junhua-best/H-Watch/PROGRAM/LCD/lcd.c

#include "lcd.h"
#include "lcd_init.h"
#include "lcdfont.h"

#include "spi.h"

/******************************************************************************
      函数说明：在指定区域填充颜色
      入口数据：xsta,ysta   起始坐标
                xend,yend   终止坐标
								color       要填充的颜色
      返回值：  无
******************************************************************************/

void LCD_Fill(uint16_t xsta,uint16_t ysta,uint16_t xend,uint16_t yend,uint16_t color)
{      
	uint16_t i,j; 
	uint8_t an[(xend-xsta)*2];
	uint32_t k=0;
	
	LCD_Address_Set(xsta,ysta,xend-1,yend-1);//设置显示范围
	
	for(i=ysta;i<yend;i++)
	{													   	 	
		for(j=xsta;j<xend;j++)
		{
			an[k] = color>>8;
			an[k+1]= color - (an[k]<<8);
			k=k+2;		
		}
		HAL_SPI_Transmit(&hspi1,an,(xend-xsta)*2,10);//发送数据	
		k=0;
	}
		  	    
}


/******************************************************************************
      函数说明：在指定区域填充颜色
      入口数据：xsta,ysta   起始坐标
                xend,yend   终止坐标
								color       要填充的颜色
         原版函数
******************************************************************************/
/*
void LCD_Fill(uint16_t xsta,uint16_t ysta,uint16_t xend,uint16_t yend,uint16_t color)
{          
	uint16_t i,j; 
	LCD_Address_Set(xsta,ysta,xend-1,yend-1);//设置显示范围
	for(i=ysta;i<yend;i++)
	{													   	 	
		for(j=xsta;j<xend;j++)
		{
			LCD_WR_DATA(color);
		}
	} 					  	    
}
*/
/******************************************************************************
      函数说明：在指定位置画点
      入口数据：x,y 画点坐标
                color 点的颜色
      返回值：  无
******************************************************************************/
void LCD_DrawPoint(uint16_t x,uint16_t y,uint16_t color)
{
	LCD_Address_Set(x,y,x,y);//设置光标位置 
	LCD_WR_DATA(color);
} 


/******************************************************************************
      函数说明：画线
      入口数据：x1,y1   起始坐标
                x2,y2   终止坐标
                color   线的颜色
      返回值：  无
******************************************************************************/
void LCD_DrawLine(uint16_t x1,uint16_t y1,uint16_t x2,uint16_t y2,uint16_t color)
{
	uint16_t t; 
	int xerr=0,yerr=0,delta_x,delta_y,distance;
	int incx,incy,uRow,uCol;
	delta_x=x2-x1; //计算坐标增量 
	delta_y=y2-y1;
	uRow=x1;//画线起点坐标
	uCol=y1;
	if(delta_x>0)incx=1; //设置单步方向 
	else if (delta_x==0)incx=0;//垂直线 
	else {incx=-1;delta_x=-delta_x;}
	if(delta_y>0)incy=1;
	else if (delta_y==0)incy=0;//水平线 
	else {incy=-1;delta_y=-delta_y;}
	if(delta_x>delta_y)distance=delta_x; //选取基本增量坐标轴 
	else distance=delta_y;
	for(t=0;t<distance+1;t++)
	{
		LCD_DrawPoint(uRow,uCol,color);//画点
		xerr+=delta_x;
		yerr+=delta_y;
		if(xerr>distance)
		{
			xerr-=distance;
			uRow+=incx;
		}
		if(yerr>distance)
		{
			yerr-=distance;
			uCol+=incy;
		}
	}
}


/******************************************************************************
      函数说明：画矩形
      入口数据：x1,y1   起始坐标
                x2,y2   终止坐标
                color   矩形的颜色
      返回值：  无
******************************************************************************/
void LCD_DrawRectangle(uint16_t x1, uint16_t y1, uint16_t x2, uint16_t y2,uint16_t color)
{
	LCD_DrawLine(x1,y1,x2,y1,color);
	LCD_DrawLine(x1,y1,x1,y2,color);
	LCD_DrawLine(x1,y2,x2,y2,color);
	LCD_DrawLine(x2,y1,x2,y2,color);
}


/******************************************************************************
      函数说明：画圆
      入口数据：x0,y0   圆心坐标
                r       半径
                color   圆的颜色
      返回值：  无
******************************************************************************/
void Draw_Circle(uint16_t x0,uint16_t y0,uint8_t r,uint16_t color)
{
	int a,b;
	a=0;b=r;	  
	while(a<=b)
	{
		LCD_DrawPoint(x0-b,y0-a,color);             //3           
		LCD_DrawPoint(x0+b,y0-a,color);             //0           
		LCD_DrawPoint(x0-a,y0+b,color);             //1                
		LCD_DrawPoint(x0-a,y0-b,color);             //2             
		LCD_DrawPoint(x0+b,y0+a,color);             //4               
		LCD_DrawPoint(x0+a,y0-b,color);             //5
		LCD_DrawPoint(x0+a,y0+b,color);             //6 
		LCD_DrawPoint(x0-b,y0+a,color);             //7
		a++;
		if((a*a+b*b)>(r*r))//判断要画的点是否过远
		{
			b--;
		}
	}
}

/******************************************************************************
      函数说明：显示汉字串
      入口数据：x,y显示坐标
                *s 要显示的汉字串
                fc 字的颜色
                bc 字的背景色
                sizey 字号 可选 16 24 32
                mode:  0非叠加模式  1叠加模式
      返回值：  无
******************************************************************************/
void LCD_ShowChinese(uint16_t x,uint16_t y,uint8_t *s,uint16_t fc,uint16_t bc,uint8_t sizey,uint8_t mode)
{
	while(*s!=0)
	{
		if(sizey==12) LCD_ShowChinese12x12(x,y,s,fc,bc,sizey,mode);
		else if(sizey==16) LCD_ShowChinese16x16(x,y,s,fc,bc,sizey,mode);
		else if(sizey==24) LCD_ShowChinese24x24(x,y,s,fc,bc,sizey,mode);
		else if(sizey==32) LCD_ShowChinese32x32(x,y,s,fc,bc,sizey,mode);
		else return;
		s+=2;
		x+=sizey;
	}
}

/******************************************************************************
      函数说明：显示单个12x12汉字
      入口数据：x,y显示坐标
                *s 要显示的汉字
                fc 字的颜色
                bc 字的背景色
                sizey 字号
                mode:  0非叠加模式  1叠加模式
      返回值：  无
******************************************************************************/
void LCD_ShowChinese12x12(uint16_t x,uint16_t y,uint8_t *s,uint16_t fc,uint16_t bc,uint8_t sizey,uint8_t mode)
{
	uint8_t i,j,m=0;
	uint16_t k;
	uint16_t HZnum;//汉字数目
	uint16_t TypefaceNum;//一个字符所占字节大小
	uint16_t x0=x;
	TypefaceNum=(sizey/8+((sizey%8)?1:0))*sizey;
	                         
	HZnum=sizeof(tfont12)/sizeof(typFNT_GB12);	//统计汉字数目
	for(k=0;k<HZnum;k++) 
	{
		if((tfont12[k].Index[0]==*(s))&&(tfont12[k].Index[1]==*(s+1)))
		{ 	
			LCD_Address_Set(x,y,x+sizey-1,y+sizey-1);
			for(i=0;i<TypefaceNum;i++)
			{
				for(j=0;j<8;j++)
				{	
					if(!mode)//非叠加方式
					{
						if(tfont12[k].Msk[i]&(0x01<<j))LCD_WR_DATA(fc);
						else LCD_WR_DATA(bc);
						m++;
						if(m%sizey==0)
						{
							m=0;
							break;
						}
					}
					else//叠加方式
					{
						if(tfont12[k].Msk[i]&(0x01<<j))	LCD_DrawPoint(x,y,fc);//画一个点
						x++;
						if((x-x0)==sizey)
						{
							x=x0;
							y++;
							break;
						}
					}
				}
			}
		}				  	
		continue;  //查找到对应点阵字库立即退出，防止多个汉字重复取模带来影响
	}
} 

/******************************************************************************
      函数说明：显示单个16x16汉字
      入口数据：x,y显示坐标
                *s 要显示的汉字
                fc 字的颜色
                bc 字的背景色
                sizey 字号
                mode:  0非叠加模式  1叠加模式
      返回值：  无
******************************************************************************/
void LCD_ShowChinese16x16(uint16_t x,uint16_t y,uint8_t *s,uint16_t fc,uint16_t bc,uint8_t sizey,uint8_t mode)
{
	uint8_t i,j,m=0;
	uint16_t k;
	uint16_t HZnum;//汉字数目
	uint16_t TypefaceNum;//一个字符所占字节大小
	uint16_t x0=x;
  TypefaceNum=(sizey/8+((sizey%8)?1:0))*sizey;
	HZnum=sizeof(tfont16)/sizeof(typFNT_GB16);	//统计汉字数目
	for(k=0;k<HZnum;k++) 
	{
		if ((tfont16[k].Index[0]==*(s))&&(tfont16[k].Index[1]==*(s+1)))
		{ 	
			LCD_Address_Set(x,y,x+sizey-1,y+sizey-1);
			for(i=0;i<TypefaceNum;i++)
			{
				for(j=0;j<8;j++)
				{	
					if(!mode)//非叠加方式
					{
						if(tfont16[k].Msk[i]&(0x01<<j))LCD_WR_DATA(fc);
						else LCD_WR_DATA(bc);
						m++;
						if(m%sizey==0)
						{
							m=0;
							break;
						}
					}
					else//叠加方式
					{
						if(tfont16[k].Msk[i]&(0x01<<j))	LCD_DrawPoint(x,y,fc);//画一个点
						x++;
						if((x-x0)==sizey)
						{
							x=x0;
							y++;
							break;
						}
					}
				}
			}
		}				  	
		continue;  //查找到对应点阵字库立即退出，防止多个汉字重复取模带来影响
	}
} 


/******************************************************************************
      函数说明：显示单个24x24汉字
      入口数据：x,y显示坐标
                *s 要显示的汉字
                fc 字的颜色
                bc 字的背景色
                sizey 字号
                mode:  0非叠加模式  1叠加模式
      返回值：  无
******************************************************************************/
void LCD_ShowChinese24x24(uint16_t x,uint16_t y,uint8_t *s,uint16_t fc,uint16_t bc,uint8_t sizey,uint8_t mode)
{
	uint8_t i,j,m=0;
	uint16_t k;
	uint16_t HZnum;//汉字数目
	uint16_t TypefaceNum;//一个字符所占字节大小
	uint16_t x0=x;
	TypefaceNum=(sizey/8+((sizey%8)?1:0))*sizey;
	HZnum=sizeof(tfont24)/sizeof(typFNT_GB24);	//统计汉字数目
	for(k=0;k<HZnum;k++) 
	{
		if ((tfont24[k].Index[0]==*(s))&&(tfont24[k].Index[1]==*(s+1)))
		{ 	
			LCD_Address_Set(x,y,x+sizey-1,y+sizey-1);
			for(i=0;i<TypefaceNum;i++)
			{
				for(j=0;j<8;j++)
				{	
					if(!mode)//非叠加方式
					{
						if(tfont24[k].Msk[i]&(0x01<<j))LCD_WR_DATA(fc);
						else LCD_WR_DATA(bc);
						m++;
						if(m%sizey==0)
						{
							m=0;
							break;
						}
					}
					else//叠加方式
					{
						if(tfont24[k].Msk[i]&(0x01<<j))	LCD_DrawPoint(x,y,fc);//画一个点
						x++;
						if((x-x0)==sizey)
						{
							x=x0;
							y++;
							break;
						}
					}
				}
			}
		}				  	
		continue;  //查找到对应点阵字库立即退出，防止多个汉字重复取模带来影响
	}
} 

/******************************************************************************
      函数说明：显示单个32x32汉字
      入口数据：x,y显示坐标
                *s 要显示的汉字
                fc 字的颜色
                bc 字的背景色
                sizey 字号
                mode:  0非叠加模式  1叠加模式
      返回值：  无
******************************************************************************/
void LCD_ShowChinese32x32(uint16_t x,uint16_t y,uint8_t *s,uint16_t fc,uint16_t bc,uint8_t sizey,uint8_t mode)
{
	uint8_t i,j,m=0;
	uint16_t k;
	uint16_t HZnum;//汉字数目
	uint16_t TypefaceNum;//一个字符所占字节大小
	uint16_t x0=x;
	TypefaceNum=(sizey/8+((sizey%8)?1:0))*sizey;
	HZnum=sizeof(tfont32)/sizeof(typFNT_GB32);	//统计汉字数目
	for(k=0;k<HZnum;k++) 
	{
		if ((tfont32[k].Index[0]==*(s))&&(tfont32[k].Index[1]==*(s+1)))
		{ 	
			LCD_Address_Set(x,y,x+sizey-1,y+sizey-1);
			for(i=0;i<TypefaceNum;i++)
			{
				for(j=0;j<8;j++)
				{	
					if(!mode)//非叠加方式
					{
						if(tfont32[k].Msk[i]&(0x01<<j))LCD_WR_DATA(fc);
						else LCD_WR_DATA(bc);
						m++;
						if(m%sizey==0)
						{
							m=0;
							break;
						}
					}
					else//叠加方式
					{
						if(tfont32[k].Msk[i]&(0x01<<j))	LCD_DrawPoint(x,y,fc);//画一个点
						x++;
						if((x-x0)==sizey)
						{
							x=x0;
							y++;
							break;
						}
					}
				}
			}
		}				  	
		continue;  //查找到对应点阵字库立即退出，防止多个汉字重复取模带来影响
	}
}


/******************************************************************************
      函数说明：显示单个字符
      入口数据：x,y显示坐标
                num 要显示的字符
                fc 字的颜色
                bc 字的背景色
                sizey 字号
                mode:  0非叠加模式  1叠加模式
      返回值：  无
******************************************************************************/
void LCD_ShowChar(uint16_t x,uint16_t y,uint8_t num,uint16_t fc,uint16_t bc,uint8_t sizey,uint8_t mode)
{
	uint8_t temp,sizex,t,m=0;
	uint16_t i,TypefaceNum;//一个字符所占字节大小
	uint16_t x0=x;
	sizex=sizey/2;
	TypefaceNum=(sizex/8+((sizex%8)?1:0))*sizey;
	num=num-' ';    //得到偏移后的值
	LCD_Address_Set(x,y,x+sizex-1,y+sizey-1);  //设置光标位置 
	for(i=0;i<TypefaceNum;i++)
	{ 
		if(sizey==12)temp=ascii_1206[num][i];		       //调用6x12字体
		else if(sizey==16)temp=ascii_1608[num][i];		 //调用8x16字体
		else if(sizey==24)temp=ascii_2412[num][i];		 //调用12x24字体
		else if(sizey==32)temp=ascii_3216[num][i];		 //调用16x32字体
		else return;
		for(t=0;t<8;t++)
		{
			if(!mode)//非叠加模式
			{
				if(temp&(0x01<<t))LCD_WR_DATA(fc);
				else LCD_WR_DATA(bc);
				m++;
				if(m%sizex==0)
				{
					m=0;
					break;
				}
			}
			else//叠加模式
			{
				if(temp&(0x01<<t))LCD_DrawPoint(x,y,fc);//画一个点
				x++;
				if((x-x0)==sizex)
				{
					x=x0;
					y++;
					break;
				}
			}
		}
	}   	 	  
}


/******************************************************************************
      函数说明：显示字符串
      入口数据：x,y显示坐标
                *p 要显示的字符串
                fc 字的颜色
                bc 字的背景色
                sizey 字号
                mode:  0非叠加模式  1叠加模式
      返回值：  无
******************************************************************************/
void LCD_ShowString(uint16_t x,uint16_t y,const uint8_t *p,uint16_t fc,uint16_t bc,uint8_t sizey,uint8_t mode)
{         
	while(*p!='\0')
	{       
		LCD_ShowChar(x,y,*p,fc,bc,sizey,mode);
		x+=sizey/2;
		p++;
	}  
}


/******************************************************************************
      函数说明：显示数字
      入口数据：m底数，n指数
      返回值：  无
******************************************************************************/
uint32_t mypow(uint8_t m,uint8_t n)
{
	uint32_t result=1;	 
	while(n--)result*=m;
	return result;
}


/******************************************************************************
      函数说明：显示整数变量
      入口数据：x,y显示坐标
                num 要显示整数变量
                len 要显示的位数
                fc 字的颜色
                bc 字的背景色
                sizey 字号
      返回值：  无
******************************************************************************/
void LCD_ShowIntNum(uint16_t x,uint16_t y,uint16_t num,uint8_t len,uint16_t fc,uint16_t bc,uint8_t sizey,uint8_t mode)
{         	
	uint8_t t,temp;
	uint8_t enshow=0;
	uint8_t sizex=sizey/2;
	for(t=0;t<len;t++)
	{
		temp=(num/mypow(10,len-t-1))%10;
		if(enshow==0&&t<(len-1))
		{
			if(temp==0)
			{
				LCD_ShowChar(x+t*sizex,y,'0',fc,bc,sizey,mode);
				continue;
			}else enshow=1; 
		 	 
		}
	 	LCD_ShowChar(x+t*sizex,y,temp+48,fc,bc,sizey,mode);
	}
} 


/******************************************************************************
      函数说明：显示两位小数变量
      入口数据：x,y显示坐标
                num 要显示小数变量
                len 要显示的位数
                fc 字的颜色
                bc 字的背景色
                sizey 字号
      返回值：  无
******************************************************************************/
void LCD_ShowFloatNum1(uint16_t x,uint16_t y,float num,uint8_t len,uint16_t fc,uint16_t bc,uint8_t sizey,uint8_t mode)
{         	
	uint8_t t,temp,sizex;
	int num1;
	sizex=sizey/2;
	num1=num*100;
	for(t=0;t<len;t++)
	{
		temp=(num1/mypow(10,len-t-1))%10;
		if(t==(len-2))
		{
			LCD_ShowChar(x+(len-2)*sizex,y,'.',fc,bc,sizey,mode);
			t++;
			len+=1;
		}
	 	LCD_ShowChar(x+t*sizex,y,temp+48,fc,bc,sizey,mode);
	}
}


/******************************************************************************
      函数说明：显示图片
      入口数据：x,y起点坐标
                length 图片长度
                width  图片宽度
                pic[]  图片数组    
      返回值：  无
******************************************************************************/
void LCD_ShowPicture(uint16_t x,uint16_t y,uint16_t length,uint16_t width,const uint8_t pic[])
{
	uint32_t i,j;
	
	uint8_t an[width*2];
	
	LCD_Address_Set(x,y,x+length-1,y+width-1);
	
	for(i=0;i<length;i++)
	{
		for(j=0;j<width*2;j++)
		{
			an[j] = pic[j+i*width*2];
		}
		HAL_SPI_Transmit(&hspi1,an,width*2,10);//发送数据
	}			
}

//{
//	uint16_t i,j;
//	uint32_t k=0;
//	
//	uint8_t an[width];
//	
//	LCD_Address_Set(x,y,x+length-1,y+width-1);
//	
//	for(i=0;i<length;i++)
//	{
//		for(j=0;j<width;j++)
//		{
//			LCD_WR_DATA8(pic[k*2]);
//			LCD_WR_DATA8(pic[k*2+1]);
//			k++;
//		}
//	}			
//}HAL_SPI_Transmit(&hspi1,an,length*width,10);//发送数据
/******************************************************************************
      函数说明：显示图片
      入口数据：x,y起点坐标
                length 图片长度
                width  图片宽度
                pic[]  图片数组    
      返回值：  无
******************************************************************************/
void LCD_ShowPicture_no_wite(uint16_t x,uint16_t y,uint16_t length,uint16_t width,const uint8_t pic[])
{
	uint16_t i,j;
	uint32_t k=0;
	uint8_t dat_buffer[2];
	for(i=y; i<y+width; i++) //根据显示原理，按照先行数后列数进行刷新
	{
		for(j=x; j<x+length; j++)//循环每行上面的像素点
		{
			if(pic[k]!= 0xFF && pic[k+1]!= 0xFF)
			{	
				LCD_Address_Set(j,i,j,i);//设置光标位置 //注意这里的横纵坐标是反着的
//				LCD_Writ_Bus(pic[k]);
//				LCD_Writ_Bus(pic[k+1]);
				dat_buffer[0] = pic[k];
				dat_buffer[1] = pic[k+1];
				HAL_SPI_Transmit_DMA(&hspi1,dat_buffer,2);//发送数据	
			}
			k = k+2;
		}
	}				
}

/******************************************************************************
      函数说明：显示图片
      入口数据：x,y起点坐标
                length 图片长度
                width  图片宽度
                pic[]  图片数组    
      返回值：  无
******************************************************************************/
void LCD_ShowPicture_no(uint16_t x,uint16_t y,uint16_t length,uint16_t width,const uint8_t pic[])
{
	uint16_t i,j;
	uint32_t k=0;
	uint8_t dat_buffer[2];
	
	for(i=y; i<y+width; i++) //根据显示原理，按照先行数后列数进行刷新
	{
		for(j=x; j<x+length; j++)//循环每行上面的像素点
		{
			LCD_Address_Set(j,i,j,i);//设置光标位置 //注意这里的横纵坐标是反着的
//			//列地址设置
//			LCD_DC_Clr();//写命令
//			LCD_Writ_Bus(0x2a);
//			LCD_DC_Set();//写数据
//					
//			dat_buffer[0] = j;
//			dat_buffer[1] = j;	
//			HAL_SPI_Transmit(&hspi1,dat_buffer,2,10);//发送数据
//			
//			
//			//行地址设置
//			LCD_DC_Clr();//写命令
//			LCD_Writ_Bus(0x2b);
//			LCD_DC_Set();//写数据
//			
//			
//			dat_buffer[0] = i+80;
//			dat_buffer[1] = i+80;	
//			HAL_SPI_Transmit(&hspi1,dat_buffer,2,10);//发送数据	
//			
//			//储存器写
//			LCD_DC_Clr();//写命令
//			LCD_Writ_Bus(0x2c);
//			LCD_DC_Set();//写数据
			
			
			dat_buffer[0] = pic[k];
			dat_buffer[1] = pic[k+1];
				
			HAL_SPI_Transmit(&hspi1,dat_buffer,2,10);//发送数据
			
					
			k = k+2;
		}
	}				
}

/******************************************************************************
      函数说明：显示图片
      入口数据：x,y起点坐标
                length 图片长度
                width  图片宽度
                pic[]  图片数组    
      返回值：  无
******************************************************************************/
void LCD_ShowPicture_clear(uint16_t x,uint16_t y,uint16_t length,uint16_t width,const uint8_t pic[])
{
	uint16_t i,j;
	uint32_t k=0;
	uint8_t dat_buffer[2];
	
	for(i=y; i<y+width; i++) //根据显示原理，按照先行数后列数进行刷新
	{
		for(j=x; j<x+length; j++)//循环每行上面的像素点
		{
			if(pic[k]!= 0xFF && pic[k+1]!= 0xFF)
			{	
//				LCD_Address_Set(j,i,j,i);//设置光标位置 //注意这里的横纵坐标是反着的
//				LCD_Writ_Bus(pic[k]);
//				LCD_Writ_Bus(pic[k+1]);
				
				//列地址设置
				LCD_DC_Clr();//写命令
				LCD_Writ_Bus(0x2a);
				LCD_DC_Set();//写数据
						
				dat_buffer[0] = j;
				dat_buffer[1] = j;	
				HAL_SPI_Transmit(&hspi1,dat_buffer,2,10);//发送数据
				
				
				//行地址设置
				LCD_DC_Clr();//写命令
				LCD_Writ_Bus(0x2b);
				LCD_DC_Set();//写数据
				
				
				dat_buffer[0] = i+80;
				dat_buffer[1] = i+80;	
				HAL_SPI_Transmit(&hspi1,dat_buffer,2,10);//发送数据	
				
				//储存器写
				LCD_DC_Clr();//写命令
				LCD_Writ_Bus(0x2c);
				LCD_DC_Set();//写数据
				
				
				dat_buffer[0] = pic[k];
				dat_buffer[1] = pic[k+1];
					
				HAL_SPI_Transmit(&hspi1,dat_buffer,2,10);//发送数据

			}
			k = k+2;
		}
	}				
}

//在指定区域内填充指定颜色块			 junhua 
//(sx,sy),(ex,ey):填充矩形对角坐标,区域大小为:(ex-sx+1)*(ey-sy+1)   
//color:要填充的颜色
/*
void LCD_Color_Fill(uint16_t sx,uint16_t sy,uint16_t ex,uint16_t ey,uint16_t *color)
{
	uint16_t height,width;
	uint16_t i,j;
	width=ex-sx+1; 			//得到填充的宽度
	height=ey-sy+1;			//高度
	//LCD_Address_Set(sx,sy,ex-1,ey-1);//设置显示范围
	//uint8_t an[(ex-sx)*2];
	//uint32_t k=0;
 	for(i=0;i<height;i++)
	{
 		
		for(j=0;j<width;j++)
		{
			
			LCD_DrawPoint(sx+j,sy+i, color[i*width+j]);
		}
		
	}
}
*/

//这种更快 设置范围只能一行一行的来

void LCD_Color_Fill(uint16_t sx,uint16_t sy,uint16_t ex,uint16_t ey,uint16_t *color)
{
	uint16_t height,width;
	uint16_t i,j;
	width=ex-sx+1; 			//得到填充的宽度
	height=ey-sy+1;			//高度
	//LCD_Address_Set(sx,sy,ex-1,ey-1);//设置显示范围
	uint8_t an[(ex-sx)*2];
	
	uint32_t k=0;
 	for(i=0;i<height;i++)
	{
 		
		LCD_Address_Set(sx,sy+i,ex-1,sy+i);//设置光标位置 
		for(j=0;j<width;j++)
		{
			
			//LCD_WR_DATA(color[i*width+j]);
			//写入数据  参考原来LCD_Fill的写法
			
			an[k] = color[i*width+j]>>8;
			an[k+1]= color[i*width+j] - (an[k]<<8);
			k=k+2;		
		
		}
		HAL_SPI_Transmit(&hspi1,an,(ex-sx)*2,10);//发送数据	
		k=0;
	}
}
