junhua-best/H-Watch/PROGRAM/LCD/pic.h

#ifndef __PIC_H
#define __PIC_H

const unsigned char gImage_shadian[512] = { /* 0X10,0X10,0X00,0X10,0X00,0X10,0X01,0X1B, */
0XFF,0X80,0XFF,0X80,0XFF,0X80,0XFF,0X80,0XFF,0X80,0XFF,0X80,0XFF,0X80,0XFF,0X80,
0XFF,0X80,0XFF,0X80,0XFF,0X62,0XFF,0X23,0XF6,0XD4,0XFF,0X80,0XFF,0X80,0XFF,0X80,
0XFF,0X80,0XFF,0X80,0XFF,0X80,0XFF,0X80,0XFF,0X80,0XFF,0X80,0XFF,0X80,0XFF,0X80,
0XFF,0X80,0XFF,0X02,0XED,0X4E,0XF5,0XEE,0XFF,0X80,0XFF,0X80,0XFF,0X80,0XFF,0X80,
0XFF,0X80,0XFF,0X80,0XFF,0X80,0XFF,0X80,0XFF,0X80,0XFF,0X80,0XFF,0X80,0XFF,0X80,
0XFF,0X00,0XEB,0X87,0XF4,0XC7,0XFF,0X40,0XFF,0X80,0XFF,0X80,0XFF,0X80,0XFF,0X80,
0XFF,0X80,0XFF,0X80,0XFF,0X80,0XFF,0X80,0XFF,0X80,0XFF,0X80,0XFF,0X80,0XFF,0X80,
0XD9,0X00,0XEB,0X84,0XFF,0X40,0XFF,0X80,0XFF,0X80,0XFF,0X80,0XFF,0X80,0XFF,0X80,
0XFF,0X80,0XFF,0X80,0XFF,0X80,0XFF,0X80,0XFF,0X80,0XFF,0X41,0XF5,0X6C,0XD1,0X04,
0XEB,0XA7,0XFF,0X80,0XFF,0X80,0XFF,0X80,0XFF,0X80,0XFF,0X80,0XFF,0X80,0XFF,0X80,
0XFF,0X80,0XFF,0X80,0XFF,0X80,0XFF,0X80,0XFE,0XE9,0XEB,0XE4,0XD9,0X04,0XEC,0X30,
0XF6,0X87,0XFE,0X67,0XFE,0X87,0XF6,0X67,0XF6,0X26,0XFE,0XE5,0XFF,0X80,0XFF,0X80,
0XFF,0X80,0XFF,0X80,0XFF,0X80,0XFD,0X68,0XDA,0X49,0XD0,0X20,0XD8,0X41,0XDA,0X08,
0XD9,0XE7,0XD9,0XC7,0XE1,0XC7,0XD9,0XC7,0XD9,0XC7,0XFD,0XEC,0XFF,0X80,0XFF,0X80,
0XFF,0X80,0XFF,0X80,0XF6,0X2B,0XD9,0X24,0XD9,0X24,0XE1,0XE7,0XD9,0X86,0XE1,0XE7,
0XE2,0X28,0XD8,0X00,0XD0,0X00,0XD9,0X04,0XF6,0X56,0XFF,0X41,0XFF,0X80,0XFF,0X80,
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
0XFF,0XFF,0XFF,0XFF,0XFF,0XFF,0XFF,0XFF,0XFF,0XFF,0XFF,0XFF,0XFF,0XFF,0XFF,0XFF,
0XFF,0XFF,0XFF,0XFF,0XFF,0XFF,0X55,0X08,0X55,0X08,0XFF,0XFF,0XFF,0XFF,0XFF,0XFF,
0XFF,0XFF,0XFF,0XFF,0XFF,0XFF,0XFF,0XFF,0XFF,0XFF,0XFF,0XFF,0XFF,0XFF,0XFF,0XFF,
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
