junhua-best/H-Watch/PROGRAM/TASKS/testtaskFun.c

#include "testtaskFun.h"





//测试类的函数库 //里面的函数全部都用来做测试




//测试写入字库
void fun_1(void)
{
	int j;
	int i;
//	Ymodel_process_fun();	进入死循环，循环接收
	for(j=GB2312_24X24_heiti; j<GB2312_24X24_heiti+0x003000; j=j+0x001000)//循环显示12K字节数据内容
	{
		ReadData_4096(j);
		
		/* 显示存储器内的数据 */
		for(i=0;i<4096;i++)
		{	
			printf("%x ",rdata[i]);
			
			if((i+1)%8 == 0) printf ("   ");
			
			if((i+1)%16 == 0) printf ("\r\n%x  ",i+0x01);
		}
		printf ("\r\n------------------------------------------------------------------------------\r\n\r\n");
	}

}

//测试写入字体图片
void fun_2(void)
{
		//打开W26Q64的片选信号，关闭屏幕的片选信号。
	HAL_GPIO_WritePin(FLASH_CS_GPIO_Port, FLASH_CS_Pin, GPIO_PIN_RESET);
	HAL_GPIO_WritePin(LCD_CS_GPIO_Port, LCD_CS_Pin, GPIO_PIN_SET);

	ReadData_4096(Pictures_address_NUM0); //从存储器读取数据到内存数组 rdata 中
	
	//打开W26Q64的片选信号，关闭屏幕的片选信号。
	HAL_GPIO_WritePin(FLASH_CS_GPIO_Port, FLASH_CS_Pin, GPIO_PIN_SET); //低电平选中
	HAL_GPIO_WritePin(LCD_CS_GPIO_Port, LCD_CS_Pin, GPIO_PIN_RESET);//低电平选中
	
	LCD_ShowPicture(0,185,40,50,rdata);
	
	
	HAL_Delay(2000);
	
	
	//打开W26Q64的片选信号，关闭屏幕的片选信号。
	HAL_GPIO_WritePin(FLASH_CS_GPIO_Port, FLASH_CS_Pin, GPIO_PIN_RESET);
	HAL_GPIO_WritePin(LCD_CS_GPIO_Port, LCD_CS_Pin, GPIO_PIN_SET);
	
	ReadData_4096(Pictures_address_NUM1);//从存储器读取数据到内存数组 rdata 中
	
	//打开W26Q64的片选信号，关闭屏幕的片选信号。
	HAL_GPIO_WritePin(FLASH_CS_GPIO_Port, FLASH_CS_Pin, GPIO_PIN_SET); //低电平选中
	HAL_GPIO_WritePin(LCD_CS_GPIO_Port, LCD_CS_Pin, GPIO_PIN_RESET);//低电平选中
	
	LCD_ShowPicture(0,185,40,50,rdata);
	
	HAL_Delay(2000);
	
	
	//打开W26Q64的片选信号，关闭屏幕的片选信号。
	HAL_GPIO_WritePin(FLASH_CS_GPIO_Port, FLASH_CS_Pin, GPIO_PIN_RESET);
	HAL_GPIO_WritePin(LCD_CS_GPIO_Port, LCD_CS_Pin, GPIO_PIN_SET);
	
	ReadData_4096(Pictures_address_NUM2);//从存储器读取数据到内存数组 rdata 中
	
	//打开W26Q64的片选信号，关闭屏幕的片选信号。
	HAL_GPIO_WritePin(FLASH_CS_GPIO_Port, FLASH_CS_Pin, GPIO_PIN_SET); //低电平选中
	HAL_GPIO_WritePin(LCD_CS_GPIO_Port, LCD_CS_Pin, GPIO_PIN_RESET);//低电平选中
	
	LCD_ShowPicture(0,185,40,50,rdata);
	
	HAL_Delay(2000);
	
	
	//打开W26Q64的片选信号，关闭屏幕的片选信号。
	HAL_GPIO_WritePin(FLASH_CS_GPIO_Port, FLASH_CS_Pin, GPIO_PIN_RESET);
	HAL_GPIO_WritePin(LCD_CS_GPIO_Port, LCD_CS_Pin, GPIO_PIN_SET);
	
	ReadData_4096(Pictures_address_NUM3);//从存储器读取数据到内存数组 rdata 中
	
	//打开W26Q64的片选信号，关闭屏幕的片选信号。
	HAL_GPIO_WritePin(FLASH_CS_GPIO_Port, FLASH_CS_Pin, GPIO_PIN_SET); //低电平选中
	HAL_GPIO_WritePin(LCD_CS_GPIO_Port, LCD_CS_Pin, GPIO_PIN_RESET);//低电平选中
	
	LCD_ShowPicture(0,185,40,50,rdata);
	
	HAL_Delay(2000);
	
	//打开W26Q64的片选信号，关闭屏幕的片选信号。
	HAL_GPIO_WritePin(FLASH_CS_GPIO_Port, FLASH_CS_Pin, GPIO_PIN_RESET);
	HAL_GPIO_WritePin(LCD_CS_GPIO_Port, LCD_CS_Pin, GPIO_PIN_SET);
	
	ReadData_4096(Pictures_address_NUM4);//从存储器读取数据到内存数组 rdata 中
	
	//打开W26Q64的片选信号，关闭屏幕的片选信号。
	HAL_GPIO_WritePin(FLASH_CS_GPIO_Port, FLASH_CS_Pin, GPIO_PIN_SET); //低电平选中
	HAL_GPIO_WritePin(LCD_CS_GPIO_Port, LCD_CS_Pin, GPIO_PIN_RESET);//低电平选中
	
	LCD_ShowPicture(0,185,40,50,rdata);
	
	
	
	
	HAL_Delay(2000);
	
	//打开W26Q64的片选信号，关闭屏幕的片选信号。
	HAL_GPIO_WritePin(FLASH_CS_GPIO_Port, FLASH_CS_Pin, GPIO_PIN_RESET);
	HAL_GPIO_WritePin(LCD_CS_GPIO_Port, LCD_CS_Pin, GPIO_PIN_SET);
	
	ReadData_4096(Pictures_address_NUM5);//从存储器读取数据到内存数组 rdata 中
	
	//打开W26Q64的片选信号，关闭屏幕的片选信号。
	HAL_GPIO_WritePin(FLASH_CS_GPIO_Port, FLASH_CS_Pin, GPIO_PIN_SET); //低电平选中
	HAL_GPIO_WritePin(LCD_CS_GPIO_Port, LCD_CS_Pin, GPIO_PIN_RESET);//低电平选中
	
	LCD_ShowPicture(0,185,40,50,rdata);
	
	
	HAL_Delay(2000);
	
	
	//打开W26Q64的片选信号，关闭屏幕的片选信号。
	HAL_GPIO_WritePin(FLASH_CS_GPIO_Port, FLASH_CS_Pin, GPIO_PIN_RESET);
	HAL_GPIO_WritePin(LCD_CS_GPIO_Port, LCD_CS_Pin, GPIO_PIN_SET);
	
	ReadData_4096(Pictures_address_NUM6);//从存储器读取数据到内存数组 rdata 中
	
	//打开W26Q64的片选信号，关闭屏幕的片选信号。
	HAL_GPIO_WritePin(FLASH_CS_GPIO_Port, FLASH_CS_Pin, GPIO_PIN_SET); //低电平选中
	HAL_GPIO_WritePin(LCD_CS_GPIO_Port, LCD_CS_Pin, GPIO_PIN_RESET);//低电平选中
	
	LCD_ShowPicture(0,185,40,50,rdata);
	
  HAL_Delay(2000);

	
	//打开W26Q64的片选信号，关闭屏幕的片选信号。
	HAL_GPIO_WritePin(FLASH_CS_GPIO_Port, FLASH_CS_Pin, GPIO_PIN_RESET);
	HAL_GPIO_WritePin(LCD_CS_GPIO_Port, LCD_CS_Pin, GPIO_PIN_SET);
	
	ReadData_4096(Pictures_address_NUM7);//从存储器读取数据到内存数组 rdata 中
	
	//打开W26Q64的片选信号，关闭屏幕的片选信号。
	HAL_GPIO_WritePin(FLASH_CS_GPIO_Port, FLASH_CS_Pin, GPIO_PIN_SET); //低电平选中
	HAL_GPIO_WritePin(LCD_CS_GPIO_Port, LCD_CS_Pin, GPIO_PIN_RESET);//低电平选中
	
	LCD_ShowPicture(0,185,40,50,rdata);
	
  HAL_Delay(2000);

	
	
	//打开W26Q64的片选信号，关闭屏幕的片选信号。
	HAL_GPIO_WritePin(FLASH_CS_GPIO_Port, FLASH_CS_Pin, GPIO_PIN_RESET);
	HAL_GPIO_WritePin(LCD_CS_GPIO_Port, LCD_CS_Pin, GPIO_PIN_SET);

	ReadData_4096(Pictures_address_NUM8);//从存储器读取数据到内存数组 rdata 中
	
	//打开W26Q64的片选信号，关闭屏幕的片选信号。
	HAL_GPIO_WritePin(FLASH_CS_GPIO_Port, FLASH_CS_Pin, GPIO_PIN_SET); //低电平选中
	HAL_GPIO_WritePin(LCD_CS_GPIO_Port, LCD_CS_Pin, GPIO_PIN_RESET);//低电平选中
	
	LCD_ShowPicture(0,185,40,50,rdata);
	
	HAL_Delay(2000);

	
	//打开W26Q64的片选信号，关闭屏幕的片选信号。
	HAL_GPIO_WritePin(FLASH_CS_GPIO_Port, FLASH_CS_Pin, GPIO_PIN_RESET);
	HAL_GPIO_WritePin(LCD_CS_GPIO_Port, LCD_CS_Pin, GPIO_PIN_SET);
//	for(i=0; i<4096; i++)
//	{
//		pictures_buffer[i] = gImage_9[i];
//	}
//	
//	WriteData_4096(Pictures_address_NUM9,pictures_buffer);//将读取到的数据写入存储器
	ReadData_4096(Pictures_address_NUM9);//从存储器读取数据到内存数组 rdata 中
	
	//打开W26Q64的片选信号，关闭屏幕的片选信号。
	HAL_GPIO_WritePin(FLASH_CS_GPIO_Port, FLASH_CS_Pin, GPIO_PIN_SET); //低电平选中
	HAL_GPIO_WritePin(LCD_CS_GPIO_Port, LCD_CS_Pin, GPIO_PIN_RESET);//低电平选中
	
	LCD_ShowPicture(0,185,40,50,rdata);
	
	HAL_Delay(2000);

}


void animations(void)
{}


	
const unsigned char gImage_t1[18000] = { /* 0X10,0X10,0X00,0X5A,0X00,0X64,0X01,0X1B, */
0XDF,0X3E,0XDF,0X3E,0XDF,0X3E,0XDF,0X3E,0XDF,0X3E,0XDF,0X3E,0XDF,0X3E,0XDF,0X3E,
0XDF,0X3E,0XDF,0X3E,0XDF,0X3E,0XDF,0X3E,0XDF,0X3E,0XDF,0X3E,0XDF,0X3E,0XDF,0X3E,
0XDF,0X3E,0XDF,0X3E,0XDF,0X3E,0XDF,0X3E,0XDF,0X3E,0XDF,0X3E,0XDF,0X3E,0XDF,0X3E,
0XDF,0X3E,0XDF,0X3E,0XDF,0X3E,0XDF,0X3E,0XDF,0X3E,0XDF,0X3E,0XDF,0X3E,0XDF,0X3E,
0XDF,0X3E,0XDF,0X3E,0XDF,0X3E,0XDF,0X3E,0XDF,0X3E,0XDF,0X3E,0XDF,0X3E,0XDF,0X3E,
0XDF,0X3E,0XDF,0X3E,0XDF,0X3E,0XDF,0X3E,0XDF,0X3E,0XDF,0X3E,0XDF,0X3E,0XDF,0X3E,
0XDF,0X3E,0XDF,0X3E,0XDF,0X3E,0XDF,0X3E,0XDF,0X3E,0XDF,0X3E,0XDF,0X3E,0XDF,0X3E,
0XDF,0X3E,0XDF,0X3E,0XDF,0X3E,0XDF,0X3E,0XDF,0X3E,0XDF,0X3E,0XDF,0X3E,0XDF,0X3E,
0XDF,0X3E,0XDF,0X3E,0XDF,0X3E,0XDF,0X3E,0XDF,0X3E,0XDF,0X3E,0XDF,0X3E,0XDF,0X3E,
0XDF,0X3E,0XDF,0X3E,0XDF,0X3E,0XDF,0X3E,0XDF,0X3E,0XDF,0X3E,0XDF,0X3E,0XDF,0X3E,
0XDF,0X3E,0XDF,0X3E,0XDF,0X3E,0XDF,0X3E,0XDF,0X3E,0XDF,0X3E,0XDF,0X3E,0XDF,0X3E,
0XDF,0X3E,0XDF,0X3E,0XDF,0X3E,0XDF,0X3E,0XDF,0X3E,0XDF,0X3E,0XDF,0X3E,0XDF,0X3E,
0XDF,0X3E,0XDF,0X3E,0XDF,0X3E,0XDF,0X3E,0XDF,0X3E,0XDF,0X3E,0XDF,0X3E,0XDF,0X3E,
0XDF,0X3E,0XDF,0X3E,0XDF,0X3E,0XDF,0X3E,0XDF,0X3E,0XDF,0X3E,0XDF,0X3E,0XDF,0X3E,
0XDF,0X3E,0XDF,0X3E,0XDF,0X3E,0XDF,0X3E,0XDF,0X3E,0XDF,0X3E,0XDF,0X3E,0XDF,0X3E,
0XDF,0X3E,0XDF,0X3E,0XDF,0X3E,0XDF,0X3E,0XDF,0X3E,0XDF,0X3E,0XDF,0X3E,0XDF,0X3E,
0XDF,0X3E,0XDF,0X3E,0XDF,0X3E,0XDF,0X3E,0XDF,0X3E,0XDF,0X3E,0XDF,0X3E,0XDF,0X3E,
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
0XDF,0X3E,0XDF,0X3E,0XDF,0X3E,0XDF,0X3E,0XDF,0X3E,0XDF,0X3E,0XDF,0X3E,0XDF,0X3E,
0XDF,0X3E,0XDF,0X3E,0XDF,0X3E,0XDF,0X3E,0XDF,0X3E,0XDF,0X3E,0XDF,0X3E,0XDF,0X3E,
0XDF,0X3E,0XDF,0X3E,0XDF,0X3E,0XDF,0X3E,0XDF,0X3E,0XDF,0X3E,0XDF,0X3E,0XDF,0X3E,
0XDF,0X3E,0X41,0XC8,0X08,0X01,0XE7,0X1E,0XDF,0X3E,0XDF,0X3E,0XDF,0X3E,0XDF,0X3E,
0XDF,0X3E,0XDF,0X3E,0XDF,0X3E,0XDF,0X3E,0XDF,0X3E,0XDF,0X1E,0X20,0XC6,0X63,0X2C,
0XE7,0X3E,0XDF,0X3E,0XDF,0X3E,0XDF,0X3E,0X94,0XB7,0X08,0X01,0XFF,0XFF,0XFF,0XDF,
0XFF,0XFF,0XFF,0XFF,0XFF,0XDF,0XFF,0XFF,0X21,0X22,0X00,0X20,0XF7,0X7D,0XFF,0XDF,
0XFF,0XDF,0XFF,0XFF,0X39,0XC6,0X62,0XEB,0XFF,0XFF,0XFF,0XFF,0XFF,0XFF,0XFF,0XFF,
0XFF,0XDF,0XC5,0XD5,0X10,0X63,0XE7,0X3E,0XDF,0X3E,0XDF,0X3E,0XDF,0X3E,0XDF,0X3E,
0XDF,0X3E,0XDF,0X3E,0XDF,0X3E,0XDF,0X3E,0XDF,0X3E,0XDF,0X3E,0XDF,0X3E,0XE7,0X3E,
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
